NavinduThimodya/RFID-Based-Asset-Tracking-System-for-Forklifts/Images/2 - Copy.png

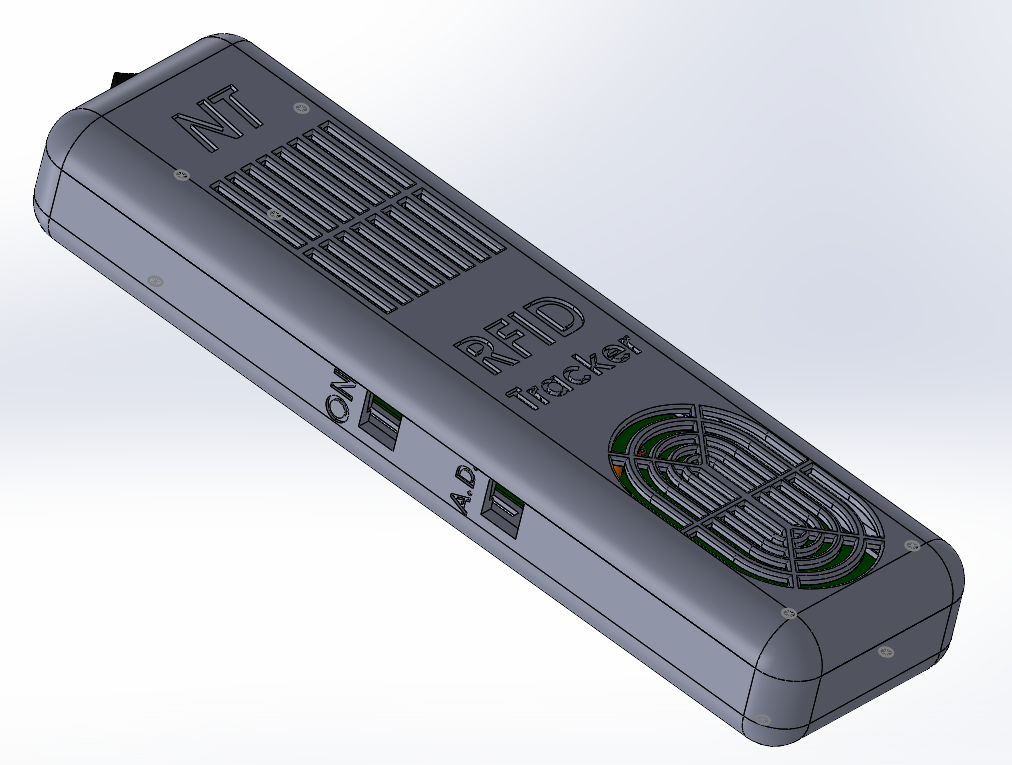
Images/2 - Copy.png
