NavinduThimodya/RFID-Based-Asset-Tracking-System-for-Forklifts/Images/4.png

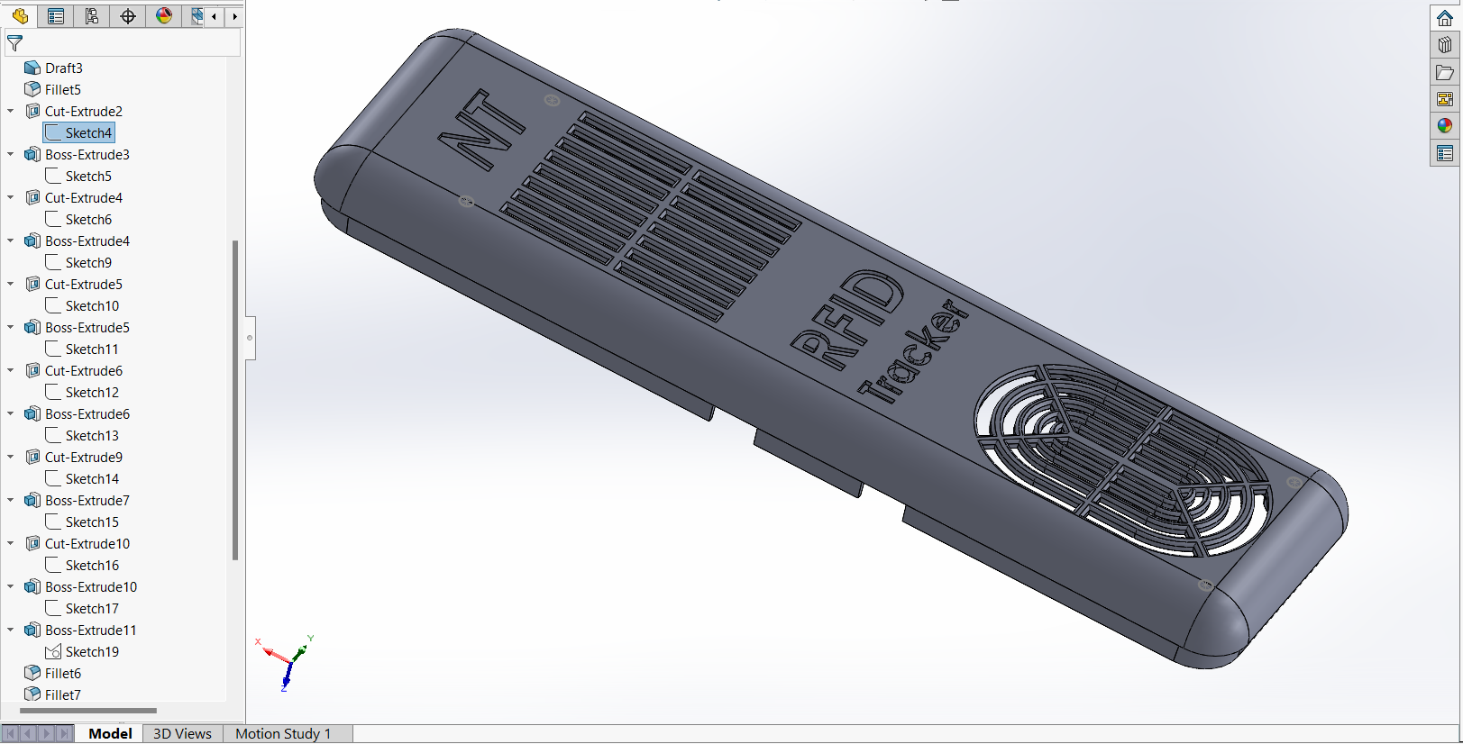
Images/4.png
