NavinduThimodya/RFID-Based-Asset-Tracking-System-for-Forklifts/Node-Red Dashboard/Screenshot 2024-09-02 005103.png

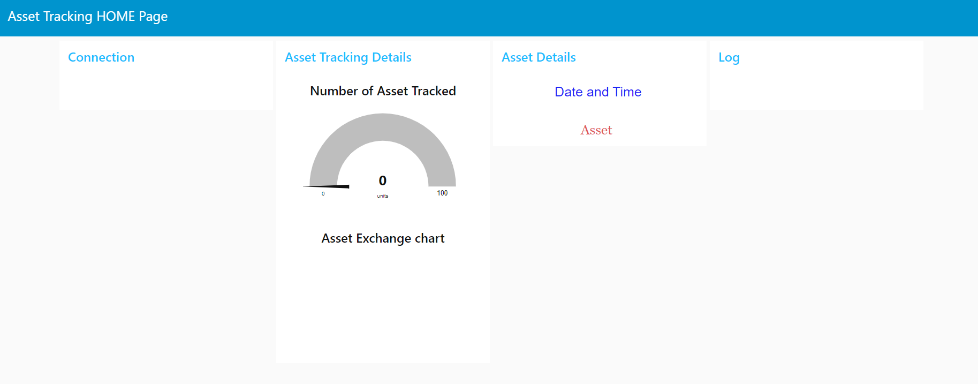
Node-Red Dashboard/Screenshot 2024-09-02 005103.png
